IdleHandsProject/samd_hcc_mod/demo_boards/canadian_flag/Flag_of_Canada_(Pantone) (1).png

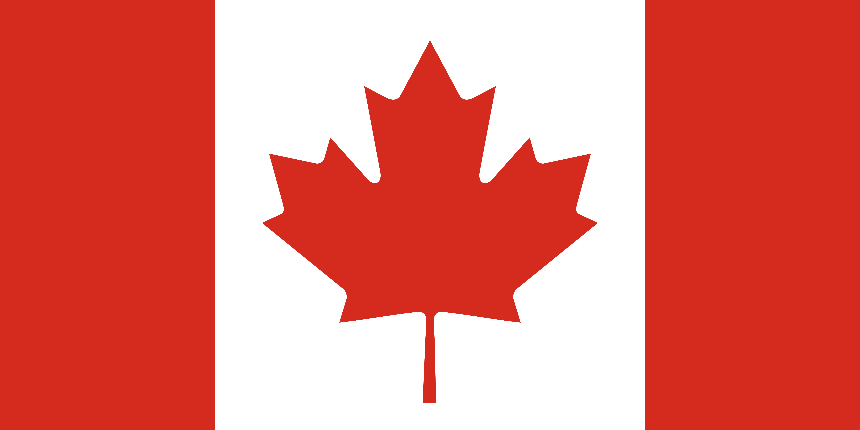
demo_boards/canadian_flag/Flag_of_Canada_(Pantone) (1).png
