IdleHandsProject/samd_hcc_mod/demo_boards/hackster_breakout/images/Hackster_thumb.png

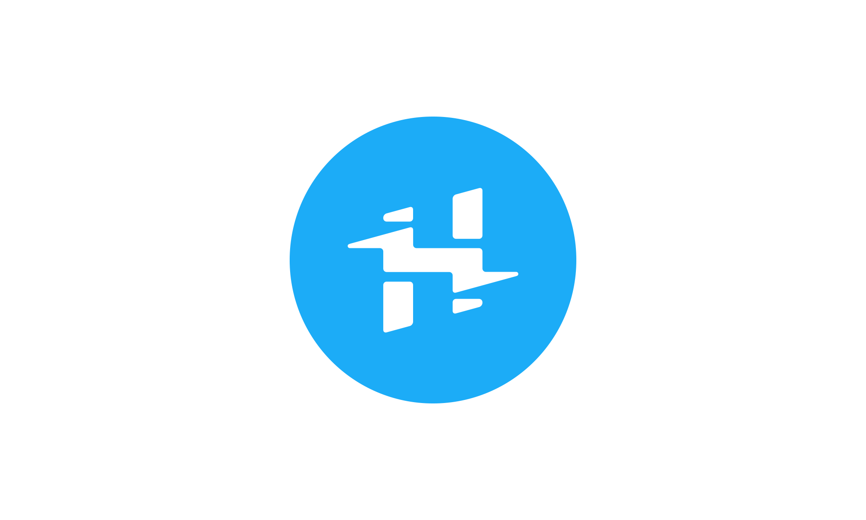
demo_boards/hackster_breakout/images/Hackster_thumb.png
