IdleHandsProject/samd_hcc_mod/demo_boards/programmer_hcc/images/1600ppi/Asset 2.png

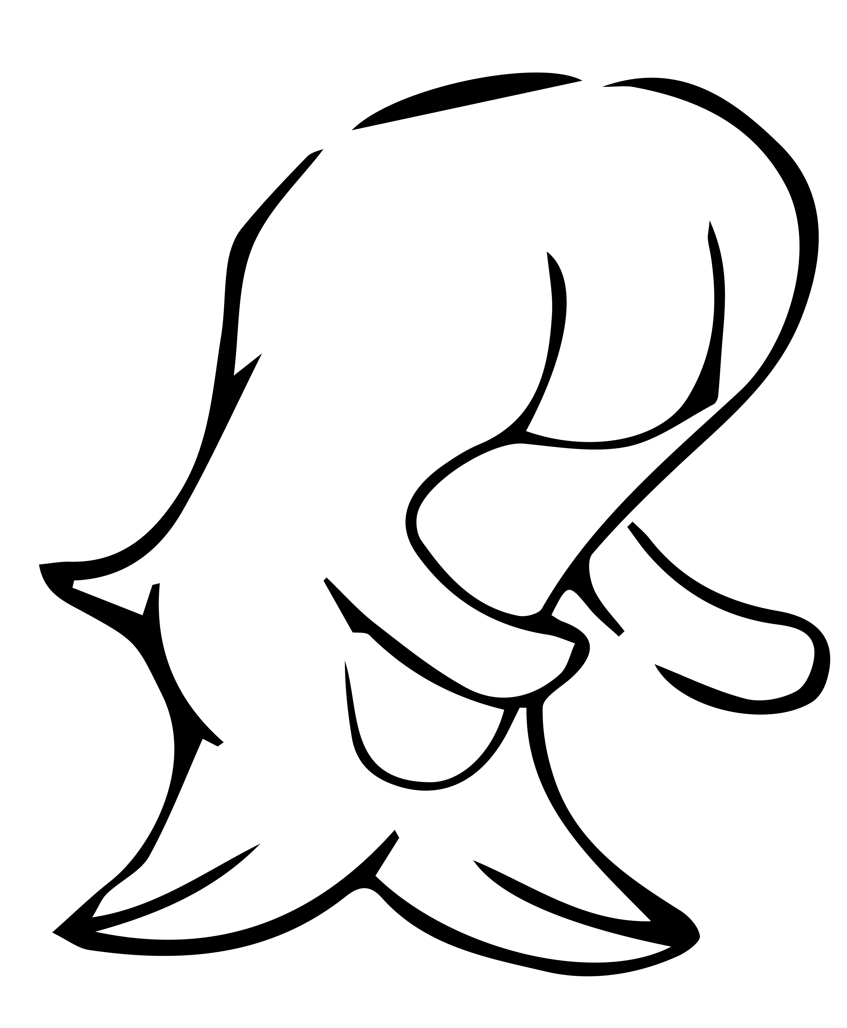
demo_boards/programmer_hcc/images/1600ppi/Asset 2.png
