IdleHandsProject/samd_hcc_mod/demo_boards/programmer_hcc/images/BOOTCOMMANDER.png

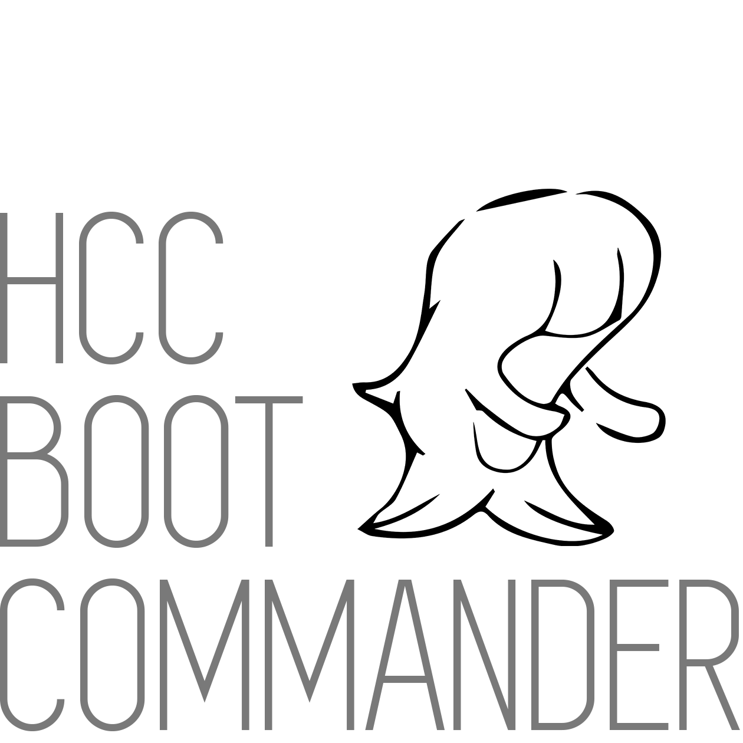
demo_boards/programmer_hcc/images/BOOTCOMMANDER.png
